AK-Homberger/ESP32-Evo-Remote-Pilot-NMEA2000/ESP32EvoPilotRemote/RaymarinePilot.h

#include "N2kMsg.h"
#include "N2kTypes.h"
#include <stdint.h>
#include <NMEA2000.h>
#include <N2kMessages.h>

enum RaymarinePilotModes {PILOT_MODE_STANDBY = 1, PILOT_MODE_AUTO = 2, PILOT_MODE_WIND = 3, PILOT_MODE_TRACK = 4};

enum key_codes {KEY_PLUS_1 = 0x07f8, KEY_PLUS_10 = 0x08f7, KEY_MINUS_1 = 0x05fa, KEY_MINUS_10 = 0x06f9, KEY_MINUS_1_MINUS_10 = 0x21de, KEY_PLUS_1_PLUS_10 = 0x22dd, KEY_TACK_PORTSIDE = KEY_MINUS_1_MINUS_10, KEY_TACK_STARBORD = KEY_PLUS_1_PLUS_10};

class RaymarinePilot {
  public:
    static double Heading, Variation;

    static int PilotMode;

    static void SetEvoPilotMode(tN2kMsg &N2kMsg, uint8_t destinationAddress, RaymarinePilotModes mode);
    static void SetEvoPilotCourse(tN2kMsg &N2kMsg, uint8_t destinationAddress, double heading, int change);
    static void TurnToWaypointMode(tN2kMsg &N2kMsg, uint8_t destinationAddress);
    static void TurnToWaypoint(tN2kMsg &N2kMsg, uint8_t destinationAddress);
    static void KeyCommand(tN2kMsg &N2kMsg, uint8_t destinationAddress, uint16_t command);

    static void SetN2kPGN65288(tN2kMsg &N2kMsg, uint8_t destinationAddress, unsigned char AlarmState, unsigned char AlarmCode, unsigned char AlarmGroup);
    static inline void SetN2kAlarmState(tN2kMsg &N2kMsg, uint8_t destinationAddress, unsigned char AlarmState, unsigned char AlarmCode, unsigned char AlarmGroup) {
      return SetN2kPGN65288(N2kMsg, destinationAddress, AlarmState, AlarmCode, AlarmGroup);
    }

    static void SetN2kPGN65361(tN2kMsg &N2kMsg, uint8_t destinationAddress, unsigned char AlarmCode, unsigned char AlarmGroup);
    static inline void SetN2kSilenceAlarm(tN2kMsg &N2kMsg, uint8_t destinationAddress, unsigned char AlarmCode, unsigned char AlarmGroup) {
      return SetN2kPGN65361(N2kMsg, destinationAddress, AlarmCode, AlarmGroup);
    }

    static void HandleNMEA2000Msg(const tN2kMsg &N2kMsg);

    static bool ParseN2kPGN65288(const tN2kMsg &N2kMsg, unsigned char &AlarmCode, unsigned char &AlarmGroup);
    static inline bool ParseN2kAlarm(const tN2kMsg &N2kMsg, unsigned char &AlarmCode, unsigned char &AlarmGroup) {
      return ParseN2kPGN65288(N2kMsg, AlarmCode, AlarmGroup);
    }


    static bool ParseN2kPGN65379(const tN2kMsg &N2kMsg, unsigned char &Mode, unsigned char &Submode);
    static inline bool ParseN2kPiloteState(const tN2kMsg &N2kMsg, unsigned char &Mode, unsigned char &Submode) {
      return ParseN2kPGN65379(N2kMsg, Mode, Submode);
    }
};
